r00li/RhomeV3/EMBLOCKS PROJECT/RHome_version3/Custom/tm_stm32f4_ili9341.c

#include "tm_stm32f4_ili9341.h"
#include "tm_stm32f4_fonts.h"

#include "FreeRTOS.h"
#include "task.h"

uint16_t ILI9341_x;
uint16_t ILI9341_y;
TM_ILI931_Options_t ILI9341_Opts;

void TM_ILI9341_Init()
{
	GPIO_InitTypeDef GPIO_InitDef;

	RCC_AHB1PeriphClockCmd(ILI9341_WRX_CLK, ENABLE);

	GPIO_InitDef.GPIO_Pin = ILI9341_WRX_PIN;
	GPIO_InitDef.GPIO_Speed = GPIO_Speed_100MHz;
	GPIO_InitDef.GPIO_Mode = GPIO_Mode_OUT;
	GPIO_InitDef.GPIO_OType = GPIO_OType_PP;
	GPIO_InitDef.GPIO_PuPd = GPIO_PuPd_NOPULL;
	GPIO_Init(ILI9341_WRX_PORT, &GPIO_InitDef);


	RCC_AHB1PeriphClockCmd(ILI9341_CS_CLK, ENABLE);
	GPIO_InitDef.GPIO_Pin = ILI9341_CS_PIN;
	GPIO_Init(ILI9341_CS_PORT, &GPIO_InitDef);


	RCC_AHB1PeriphClockCmd(ILI9341_RST_CLK, ENABLE);
	GPIO_InitDef.GPIO_PuPd = GPIO_PuPd_UP;
	GPIO_InitDef.GPIO_Pin = ILI9341_RST_PIN;
	GPIO_Init(ILI9341_RST_PORT, &GPIO_InitDef);

	ILI9341_CS_SET;

	//TM_SPI_Init(ILI9341_SPI, TM_SPI_PinsPack_1);
		  SPI_InitTypeDef  SPI_InitStructure;
		  	  GPIO_InitTypeDef GPIO_InitStructure;

		  	  	  /* Enable the SPI periph */
	  RCC_APB1PeriphClockCmd(RCC_APB1Periph_SPI2, ENABLE);

	  /* Enable SCK, MOSI and MISO GPIO clocks */
	  RCC_AHB1PeriphClockCmd(RCC_AHB1Periph_GPIOB , ENABLE);

	  GPIO_PinAFConfig(GPIOB, GPIO_PinSource13, GPIO_AF_SPI2);
	  GPIO_PinAFConfig(GPIOB, GPIO_PinSource14, GPIO_AF_SPI2);
	  GPIO_PinAFConfig(GPIOB, GPIO_PinSource15, GPIO_AF_SPI2);

	  GPIO_InitStructure.GPIO_Mode = GPIO_Mode_AF;
	  GPIO_InitStructure.GPIO_OType = GPIO_OType_PP;
	  GPIO_InitStructure.GPIO_PuPd  = GPIO_PuPd_DOWN;
	  GPIO_InitStructure.GPIO_Speed = GPIO_Speed_100MHz;

		  /* SPI pins configuration */
	  GPIO_InitStructure.GPIO_Pin = GPIO_Pin_13|GPIO_Pin_14|GPIO_Pin_15;
	  GPIO_Init(GPIOB, &GPIO_InitStructure);

	  /* SPI configuration -------------------------------------------------------*/
	  SPI_I2S_DeInit(SPI2);
	  SPI_InitStructure.SPI_Direction = SPI_Direction_2Lines_FullDuplex;
	  SPI_InitStructure.SPI_DataSize = SPI_DataSize_8b;
	  SPI_InitStructure.SPI_CPOL = SPI_CPOL_Low;
	  SPI_InitStructure.SPI_CPHA = SPI_CPHA_1Edge;
	  SPI_InitStructure.SPI_NSS = SPI_NSS_Soft;
	  SPI_InitStructure.SPI_BaudRatePrescaler = SPI_BaudRatePrescaler_2;
	  SPI_InitStructure.SPI_FirstBit = SPI_FirstBit_MSB;
	  SPI_InitStructure.SPI_CRCPolynomial = 7;
	  SPI_InitStructure.SPI_Mode = SPI_Mode_Master;
	  SPI_Init(SPI2, &SPI_InitStructure);

	  /* Enable SPI1  */
	  SPI_Cmd(SPI2, ENABLE);

	TM_ILI9341_InitLCD();

	TM_ILI9341_Fill(ILI9341_COLOR_WHITE);

	ILI9341_x = ILI9341_y = 0;

	ILI9341_Opts.width = ILI9341_WIDTH;
	ILI9341_Opts.height = ILI9341_HEIGHT;
	ILI9341_Opts.orientation = TM_ILI9341_Portrait;
}

void TM_ILI9341_InitLCD(void)
{
    taskENTER_CRITICAL();

	//ILI9341_RST_RESET;
	ILI9341_RST_SET;

	TM_ILI9341_SendCommand(ILI9341_RESET);
	TM_ILI9341_Delay(2000000);

	TM_ILI9341_SendCommand(ILI9341_POWERA);
	TM_ILI9341_SendData(0x39);
	TM_ILI9341_SendData(0x2C);
	TM_ILI9341_SendData(0x00);
	TM_ILI9341_SendData(0x34);
	TM_ILI9341_SendData(0x02);
	TM_ILI9341_SendCommand(ILI9341_POWERB);
	TM_ILI9341_SendData(0x00);
	TM_ILI9341_SendData(0xC1);
	TM_ILI9341_SendData(0x30);
	TM_ILI9341_SendCommand(ILI9341_DTCA);
	TM_ILI9341_SendData(0x85);
	TM_ILI9341_SendData(0x00);
	TM_ILI9341_SendData(0x78);
	TM_ILI9341_SendCommand(ILI9341_DTCB);
	TM_ILI9341_SendData(0x00);
	TM_ILI9341_SendData(0x00);
	TM_ILI9341_SendCommand(ILI9341_POWER_SEQ);
	TM_ILI9341_SendData(0x64);
	TM_ILI9341_SendData(0x03);
	TM_ILI9341_SendData(0x12);
	TM_ILI9341_SendData(0x81);
	TM_ILI9341_SendCommand(ILI9341_PRC);
	TM_ILI9341_SendData(0x20);
	TM_ILI9341_SendCommand(ILI9341_POWER1);
	TM_ILI9341_SendData(0x23);
	TM_ILI9341_SendCommand(ILI9341_POWER2);
	TM_ILI9341_SendData(0x10);
	TM_ILI9341_SendCommand(ILI9341_VCOM1);
	TM_ILI9341_SendData(0x3E);
	TM_ILI9341_SendData(0x28);
	TM_ILI9341_SendCommand(ILI9341_VCOM2);
	TM_ILI9341_SendData(0x86);
	TM_ILI9341_SendCommand(ILI9341_MAC);
	TM_ILI9341_SendData(0x48);
	TM_ILI9341_SendCommand(ILI9341_PIXEL_FORMAT);
	TM_ILI9341_SendData(0x55);
	TM_ILI9341_SendCommand(ILI9341_FRC);
	TM_ILI9341_SendData(0x00);
	TM_ILI9341_SendData(0x18);
	TM_ILI9341_SendCommand(ILI9341_DFC);
	TM_ILI9341_SendData(0x08);
	TM_ILI9341_SendData(0x82);
	TM_ILI9341_SendData(0x27);
	TM_ILI9341_SendCommand(ILI9341_3GAMMA_EN);
	TM_ILI9341_SendData(0x00);
	TM_ILI9341_SendCommand(ILI9341_COLUMN_ADDR);
	TM_ILI9341_SendData(0x00);
	TM_ILI9341_SendData(0x00);
	TM_ILI9341_SendData(0x00);
	TM_ILI9341_SendData(0xEF);
	TM_ILI9341_SendCommand(ILI9341_PAGE_ADDR);
	TM_ILI9341_SendData(0x00);
	TM_ILI9341_SendData(0x00);
	TM_ILI9341_SendData(0x01);
	TM_ILI9341_SendData(0x3F);
	TM_ILI9341_SendCommand(ILI9341_GAMMA);
	TM_ILI9341_SendData(0x01);
	TM_ILI9341_SendCommand(ILI9341_PGAMMA);
	TM_ILI9341_SendData(0x0F);
	TM_ILI9341_SendData(0x31);
	TM_ILI9341_SendData(0x2B);
	TM_ILI9341_SendData(0x0C);
	TM_ILI9341_SendData(0x0E);
	TM_ILI9341_SendData(0x08);
	TM_ILI9341_SendData(0x4E);
	TM_ILI9341_SendData(0xF1);
	TM_ILI9341_SendData(0x37);
	TM_ILI9341_SendData(0x07);
	TM_ILI9341_SendData(0x10);
	TM_ILI9341_SendData(0x03);
	TM_ILI9341_SendData(0x0E);
	TM_ILI9341_SendData(0x09);
	TM_ILI9341_SendData(0x00);
	TM_ILI9341_SendCommand(ILI9341_NGAMMA);
	TM_ILI9341_SendData(0x00);
	TM_ILI9341_SendData(0x0E);
	TM_ILI9341_SendData(0x14);
	TM_ILI9341_SendData(0x03);
	TM_ILI9341_SendData(0x11);
	TM_ILI9341_SendData(0x07);
	TM_ILI9341_SendData(0x31);
	TM_ILI9341_SendData(0xC1);
	TM_ILI9341_SendData(0x48);
	TM_ILI9341_SendData(0x08);
	TM_ILI9341_SendData(0x0F);
	TM_ILI9341_SendData(0x0C);
	TM_ILI9341_SendData(0x31);
	TM_ILI9341_SendData(0x36);
	TM_ILI9341_SendData(0x0F);
	TM_ILI9341_SendCommand(ILI9341_SLEEP_OUT);

	TM_ILI9341_Delay(1000000);

	TM_ILI9341_SendCommand(ILI9341_DISPLAY_ON);
	TM_ILI9341_SendCommand(ILI9341_GRAM);

	taskEXIT_CRITICAL();
}

void SPI_Transfer(uint8_t data)
{

  while(SPI_I2S_GetFlagStatus(SPI2,SPI_I2S_FLAG_TXE)==RESET){}
  SPI_I2S_SendData(SPI2, data);
  while (SPI_I2S_GetFlagStatus(SPI2, SPI_I2S_FLAG_RXNE) == RESET){}
  SPI_I2S_ReceiveData(SPI2);

}

void TM_ILI9341_SendCommand(uint8_t data)
{
	ILI9341_WRX_RESET;
	ILI9341_CS_RESET;
	//TM_SPI_Send(ILI9341_SPI, data);
	SPI_Transfer(data);
	ILI9341_CS_SET;
}

void TM_ILI9341_SendData(uint8_t data)
{
	ILI9341_WRX_SET;
	ILI9341_CS_RESET;
	//TM_SPI_Send(ILI9341_SPI, data);
	SPI_Transfer(data);
	ILI9341_CS_SET;

}

void TM_ILI9341_DrawPixel(uint16_t x, uint16_t y, uint16_t color)
{
	TM_ILI9341_SetCursorPosition(x, y, x, y);

	TM_ILI9341_SendCommand(ILI9341_GRAM);
	TM_ILI9341_SendData(color >> 8);
	TM_ILI9341_SendData(color & 0xFF);
}


void TM_ILI9341_SetCursorPosition(uint16_t x1, uint16_t y1, uint16_t x2, uint16_t y2)
{
	TM_ILI9341_SendCommand(ILI9341_COLUMN_ADDR);
	TM_ILI9341_SendData(x1 >> 8);
	TM_ILI9341_SendData(x1 & 0xFF);
	TM_ILI9341_SendData(x2 >> 8);
	TM_ILI9341_SendData(x2 & 0xFF);

	TM_ILI9341_SendCommand(ILI9341_PAGE_ADDR);
	TM_ILI9341_SendData(y1 >> 8);
	TM_ILI9341_SendData(y1 & 0xFF);
	TM_ILI9341_SendData(y2 >> 8);
	TM_ILI9341_SendData(y2 & 0xFF);
}

void TM_ILI9341_Fill(uint16_t color)
{
	unsigned int n, i, j;
	i = color >> 8;
	j = color & 0xFF;
	TM_ILI9341_SetCursorPosition(0, 0, ILI9341_Opts.width - 1, ILI9341_Opts.height - 1);

	TM_ILI9341_SendCommand(ILI9341_GRAM);

	for (n = 0; n < ILI9341_PIXEL; n++) {
		TM_ILI9341_SendData(i);
		TM_ILI9341_SendData(j);
	}

}

void TM_ILI9341_Delay(volatile unsigned int delay)
{
	for (; delay != 0; delay--);
}

void TM_ILI9341_Rotate(TM_ILI9341_Orientation_t orientation)
{
	TM_ILI9341_SendCommand(ILI9341_MAC);
	if (orientation == TM_ILI9341_Orientation_Portrait_1) {
		TM_ILI9341_SendData(0x58);
	} else if (orientation == TM_ILI9341_Orientation_Portrait_2) {
		TM_ILI9341_SendData(0x88);
	} else if (orientation == TM_ILI9341_Orientation_Landscape_1) {
		TM_ILI9341_SendData(0x28);
	} else if (orientation == TM_ILI9341_Orientation_Landscape_2) {
		TM_ILI9341_SendData(0xE8);
	}

	if (orientation == TM_ILI9341_Orientation_Portrait_1 || orientation == TM_ILI9341_Orientation_Portrait_2) {
		ILI9341_Opts.width = ILI9341_WIDTH;
		ILI9341_Opts.height = ILI9341_HEIGHT;
		ILI9341_Opts.orientation = TM_ILI9341_Portrait;
	} else {
		ILI9341_Opts.width = ILI9341_HEIGHT;
		ILI9341_Opts.height = ILI9341_WIDTH;
		ILI9341_Opts.orientation = TM_ILI9341_Landscape;
	}
}

void TM_ILI9341_Puts(uint16_t x, uint16_t y, char *str, TM_FontDef_t *font, uint16_t foreground, uint16_t background)
{
    taskENTER_CRITICAL();

	uint16_t startX = x;
	ILI9341_x = x;
	ILI9341_y = y;

	while (*str) {
		//New line
		if (*str == '\n') {
			ILI9341_y += font->FontHeight + 1;
			//if after \n is also \r, than go to the left of the screen
			if (*(str + 1) == '\r') {
				ILI9341_x = 0;
				str++;
			} else {
				ILI9341_x = startX;
			}
			str++;
			continue;
		} else if (*str == '\r') {
			str++;
			continue;
		}

		TM_ILI9341_Putc(ILI9341_x, ILI9341_y, *str++, font, foreground, background);
	}

	taskEXIT_CRITICAL();
}

void TM_ILI9341_GetStringSize(char *str, TM_FontDef_t *font, uint16_t *width, uint16_t *height)
{
	uint16_t w = 0;
	*height = font->FontHeight;
	while (*str++) {
		w += font->FontWidth;
	}
	*width = w;
}

void TM_ILI9341_Putc(uint16_t x, uint16_t y, char c, TM_FontDef_t *font, uint16_t foreground, uint16_t background)
{
	uint32_t i, b, j;
	if ((ILI9341_x + font->FontWidth) > ILI9341_Opts.width) {
		//If at the end of a line of display, go to new line and set x to 0 position
		ILI9341_y += font->FontHeight;
		ILI9341_x = 0;
	}
	for (i = 0; i < font->FontHeight; i++) {
		b = font->data[(c - 32) * font->FontHeight + i];
		for (j = 0; j < font->FontWidth; j++) {
			if ((b << j) & 0x8000) {
				TM_ILI9341_DrawPixel(ILI9341_x + j, (ILI9341_y + i), foreground);
			} else {
				TM_ILI9341_DrawPixel(ILI9341_x + j, (ILI9341_y + i), background);
			}
		}
	}
	ILI9341_x += font->FontWidth;

}


void TM_ILI9341_DrawLine(uint16_t x0, uint16_t y0, uint16_t x1, uint16_t y1, uint16_t color)
{

	short dx, dy;
	short temp;

	if (x0 > x1) {
		temp = x1;
		x1 = x0;
		x0 = temp;
	}
	if (y0 > y1) {
		temp = y1;
		y1 = y0;
		y0 = temp;
	}

	dx = x1 - x0;
	dy = y1 - y0;

	if (dx == 0) {
		do {
			TM_ILI9341_DrawPixel(x0, y0, color);
			y0++;
		} while (y1 >= y0);
		return;
	}
	if (dy == 0) {
		do {
			TM_ILI9341_DrawPixel(x0, y0, color);
			x0++;
		} while (x1 >= x0);
		return;
	}

	/* Based on Bresenham's line algorithm  */
	if (dx > dy) {
		temp = 2 * dy - dx;
		while (x0 != x1) {
			TM_ILI9341_DrawPixel(x0, y0, color);
			x0++;
			if (temp > 0) {
				y0++;
				temp += 2 * dy - 2 * dx;
			} else {
				temp += 2 * dy;
			}
		}
		TM_ILI9341_DrawPixel(x0, y0, color);
	} else {
		temp = 2 * dx - dy;
		while (y0 != y1) {
			TM_ILI9341_DrawPixel(x0, y0, color);
			y0++;
			if (temp > 0) {
				x0++;
				temp += 2 * dy - 2 * dx;
			} else {
				temp += 2 * dy;
			}
		}
		TM_ILI9341_DrawPixel(x0, y0, color);
	}

}

void TM_ILI9341_DrawRectangle(uint16_t x0, uint16_t y0, uint16_t x1, uint16_t y1, uint16_t color) {
	TM_ILI9341_DrawLine(x0, y0, x1, y0, color); //Top
	TM_ILI9341_DrawLine(x0, y0, x0, y1, color);	//Left
	TM_ILI9341_DrawLine(x1, y0, x1, y1, color);	//Right
	TM_ILI9341_DrawLine(x0, y1, x1, y1, color);	//Bottom
}

void TM_ILI9341_DrawFilledRectangle(uint16_t x0, uint16_t y0, uint16_t x1, uint16_t y1, uint16_t color)
{
	for (; y0 < y1; y0++) {
		TM_ILI9341_DrawLine(x0, y0, x1, y0, color);
	}
}

void TM_ILI9341_DrawCircle(int16_t x0, int16_t y0, int16_t r, uint16_t color)
{
	int16_t f = 1 - r;
	int16_t ddF_x = 1;
	int16_t ddF_y = -2 * r;
	int16_t x = 0;
	int16_t y = r;

    TM_ILI9341_DrawPixel(x0, y0 + r, color);
    TM_ILI9341_DrawPixel(x0, y0 - r, color);
    TM_ILI9341_DrawPixel(x0 + r, y0, color);
    TM_ILI9341_DrawPixel(x0 - r, y0, color);

    while (x < y) {
        if (f >= 0) {
            y--;
            ddF_y += 2;
            f += ddF_y;
        }
        x++;
        ddF_x += 2;
        f += ddF_x;

        TM_ILI9341_DrawPixel(x0 + x, y0 + y, color);
        TM_ILI9341_DrawPixel(x0 - x, y0 + y, color);
        TM_ILI9341_DrawPixel(x0 + x, y0 - y, color);
        TM_ILI9341_DrawPixel(x0 - x, y0 - y, color);

        TM_ILI9341_DrawPixel(x0 + y, y0 + x, color);
        TM_ILI9341_DrawPixel(x0 - y, y0 + x, color);
        TM_ILI9341_DrawPixel(x0 + y, y0 - x, color);
        TM_ILI9341_DrawPixel(x0 - y, y0 - x, color);
    }
}

void TM_ILI9341_DrawFilledCircle(int16_t x0, int16_t y0, int16_t r, uint16_t color)
{

	int16_t f = 1 - r;
	int16_t ddF_x = 1;
	int16_t ddF_y = -2 * r;
	int16_t x = 0;
	int16_t y = r;

    TM_ILI9341_DrawPixel(x0, y0 + r, color);
    TM_ILI9341_DrawPixel(x0, y0 - r, color);
    TM_ILI9341_DrawPixel(x0 + r, y0, color);
    TM_ILI9341_DrawPixel(x0 - r, y0, color);
    TM_ILI9341_DrawLine(x0 - r, y0, x0 + r, y0, color);

    while (x < y) {
        if (f >= 0) {
            y--;
            ddF_y += 2;
            f += ddF_y;
        }
        x++;
        ddF_x += 2;
        f += ddF_x;

        TM_ILI9341_DrawLine(x0 - x, y0 + y, x0 + x, y0 + y, color);
        TM_ILI9341_DrawLine(x0 + x, y0 - y, x0 - x, y0 - y, color);

        TM_ILI9341_DrawLine(x0 + y, y0 + x, x0 - y, y0 + x, color);
        TM_ILI9341_DrawLine(x0 + y, y0 - x, x0 - y, y0 - x, color);
    }

}


void TM_ILI9341_DrawFilledBrokenCircle (int poX, int poY, int r, uint16_t color)
{
    //int poX = -100;
    // int poY = 120;
    //int r = 150;

    int x = -r, y = 0, err = 2-2*r, e2;
    do
    {
        uint8_t draw = 1;
        int x_min_x = poX-x;
        if (poX-x < 0)
            draw = 0;
        //x_min_x = 0;

        int y_min_y = poY-y;
        if (poY-y < 0)
            y_min_y  = 0;

        int x_plus_x = poX+x;
        if (x_plus_x > 320)
            draw = 0;
        //x_plus_x = 320;

        int hght = y_min_y+2*y;
        if (hght > 240)
            hght = 240;


        if (draw)
        {
            //drawVerticalLine(poX-x, poY-y, 2*y, color);
            TM_ILI9341_DrawLine(x_min_x, y_min_y, x_min_x, hght, color);
            //drawVerticalLine(poX+x, poY-y, 2*y, color);
            if (x_plus_x > 0)
                TM_ILI9341_DrawLine(x_plus_x, y_min_y, x_plus_x, hght, color);
        }
        e2 = err;
        if (e2 <= y)
        {
            err += ++y*2+1;
            if (-x == y && e2 <= x) e2 = 0;
        }
        if (e2 > x) err += ++x*2+1;
    }
    while (x <= 0);

}
