r00li/RhomeV3/EMBLOCKS PROJECT/RHome_version3/RF_Switch/RemoteReceiver.cpp

/*
 * RemoteSwitch library v2.2.1 (20120314) made by Randy Simons http://randysimons.nl/
 * See RemoteReceiver.h for details.
 *
 * License: GPLv3. See license.txt
 */

#include "RemoteReceiver.h"

/*
#define bitRead(value, bit) (((value) >> (bit)) & 0x01)
#define bitSet(value, bit) ((value) |= (1UL << (bit)))
#define bitClear(value, bit) ((value) &= ~(1UL << (bit)))
#define bitWrite(value, bit, bitvalue) (bitvalue ? bitSet(value, bit) : bitClear(value, bit))
*/

/************
* RemoteReceiver
************/

int8_t RemoteReceiver::_interrupt;
volatile int8_t RemoteReceiver::_state;
uint8_t RemoteReceiver::_minRepeats;
RemoteReceiverCallBack RemoteReceiver::_callback;
bool RemoteReceiver::_inCallback = false;
bool RemoteReceiver::_enabled = false;

void RemoteReceiver::init(unsigned short minRepeats, RemoteReceiverCallBack callback) {

    //
    // Init receiver
    //
    RCC_AHB1PeriphClockCmd(RCC_AHB1Periph_GPIOD, ENABLE);
    GPIO_InitTypeDef GPIO_InitStructure;
    GPIO_InitStructure.GPIO_Mode = GPIO_Mode_IN;
    GPIO_InitStructure.GPIO_PuPd = GPIO_PuPd_NOPULL;
    GPIO_InitStructure.GPIO_Pin = GPIO_Pin_6;

    GPIO_Init(GPIOD, &GPIO_InitStructure);

    RCC_APB2PeriphClockCmd(RCC_APB2Periph_SYSCFG, ENABLE);
    SYSCFG_EXTILineConfig(EXTI_PortSourceGPIOD, EXTI_PinSource6);

    EXTI_InitTypeDef EXTI_struktura;
    EXTI_struktura.EXTI_Line = EXTI_Line6;
    EXTI_struktura.EXTI_Mode = EXTI_Mode_Interrupt;
    EXTI_struktura.EXTI_Trigger = EXTI_Trigger_Rising_Falling;
    EXTI_struktura.EXTI_LineCmd = ENABLE;
    EXTI_Init(&EXTI_struktura);

    //Enable NVIC
    NVIC_InitTypeDef NVIC_InitStructure;
    NVIC_InitStructure.NVIC_IRQChannel = EXTI9_5_IRQn;
    NVIC_InitStructure.NVIC_IRQChannelPreemptionPriority = 0;
    NVIC_InitStructure.NVIC_IRQChannelSubPriority = 0;
    NVIC_InitStructure.NVIC_IRQChannelCmd = ENABLE;
    NVIC_Init(&NVIC_InitStructure);

	_minRepeats = minRepeats;
	_callback = callback;

	enable();
}

void RemoteReceiver::enable() {
	_state = -1;
	_enabled = true;
}

void RemoteReceiver::disable() {
	_enabled = false;
}


void RemoteReceiver::interruptHandler() {
	if (!_enabled) {
		return;
	}

	static unsigned int period;				// Calculated duration of 1 period
	static uint16_t receivedBit;				// Contains "bit" currently receiving
	static unsigned long receivedCode;		// Contains received code
	static unsigned long previousCode;		// Contains previous received code
	static uint8_t repeats = 0;				// The number of times the an identical code is received in a row.
	static unsigned long edgeTimeStamp[3] = {0, };	// Timestamp of edges
	static unsigned int min1Period, max1Period, min3Period, max3Period;
	static bool skip;

	// Filter out too short pulses. This method works as a low pass filter.
	edgeTimeStamp[1] = edgeTimeStamp[2];
	edgeTimeStamp[2] = micros();

	if (skip) {
		skip = false;
		return;
	}

	if (_state >= 0 && edgeTimeStamp[2]-edgeTimeStamp[1] < min1Period) {
		// Last edge was too short.
		// Skip this edge, and the next too.
		skip = true;
		return;
	}

	unsigned int duration = edgeTimeStamp[1] - edgeTimeStamp[0];
	edgeTimeStamp[0] = edgeTimeStamp[1];

	// Note that if state>=0, duration is always >= 1 period.

	if (_state==-1) { // Waiting for sync-signal
		if (duration>3720) { // =31*120 minimal time between two edges before decoding starts.
			// Sync signal received.. Preparing for decoding
			period=duration/31;
			receivedCode=previousCode=repeats=0;

			// Allow for large error-margin. ElCheapo-hardware :(
			min1Period=period*4/10; // Avoid floating point math; saves memory.
			max1Period=period*16/10;
			min3Period=period*23/10;
			max3Period=period*37/10;
		}
		else {
			return;
		}
	} else if (_state<48) { // Decoding message
		receivedBit <<= 1;

		// bit part durations can ONLY be 1 or 3 periods.
		if (duration<=max1Period) {
			receivedBit &= 0b1110; // Clear LSB of receivedBit
		}
		else if (duration>=min3Period && duration<=max3Period) {
			receivedBit |= 0b1; // Set LSB of receivedBit
		}
		else { // Otherwise the entire sequence is invalid
			_state=-1;
			return;
		}

		if ((_state%4)==3) { // Last bit part?
			// Shift
			receivedCode*=3;

			// Only 4 LSB's are used; trim the rest.
			switch (receivedBit & 0b1111) {
				case 0b0101: // short long short long == B0101
					// bit "0" received
					receivedCode+=0; // I hope the optimizer handles this ;)
					break;
				case 0b1010: // long short long short == B1010
					// bit "1" received
					receivedCode+=1;
					break;
				case 0b0110: // short long long short
					// bit "f" received
					receivedCode+=2;
					break;
				default:
					// Bit was rubbish. Abort.
					_state=-1;
					return;
			}
		}
	} else if (_state==48) { // Waiting for sync bit part 1
		// Must be 1 period.
		if (duration>max1Period) {
			_state=-1;
			return;
		}
	} else { // Waiting for sync bit part 2
		// Must be 31 periods.
		if (duration<period*25 || duration>period*36) {
		  _state=-1;
		  return;
		}

		// receivedCode is a valid code!

		if (receivedCode!=previousCode) {
			repeats=0;
			previousCode=receivedCode;
		}

		repeats++;

		if (repeats>=_minRepeats) {
			if (!_inCallback) {
				_inCallback = true;
				(_callback)(receivedCode, period);
				_inCallback = false;
			}
			// Reset after callback.
			_state=-1;
			return;
		}

		// Reset for next round
		receivedCode = 0;
		_state=0; // no need to wait for another sync-bit!
		return;
	}

	_state++;
	return;
}

bool RemoteReceiver::isReceiving(int waitMillis) {
	unsigned long startTime=millis();

	int waited; // Signed int!
	do {
		if (_state == 48) { // Abort if a valid code has been received in the mean time
			return true;
		}
		waited = (millis()-startTime);
	} while(waited>=0 && waited <= waitMillis); // Yes, clock wraps every 50 days. And then you'd have to wait for a looooong time.

	return false;
}
